ISF-H-BRS/SkinCam/Images/Software2.png

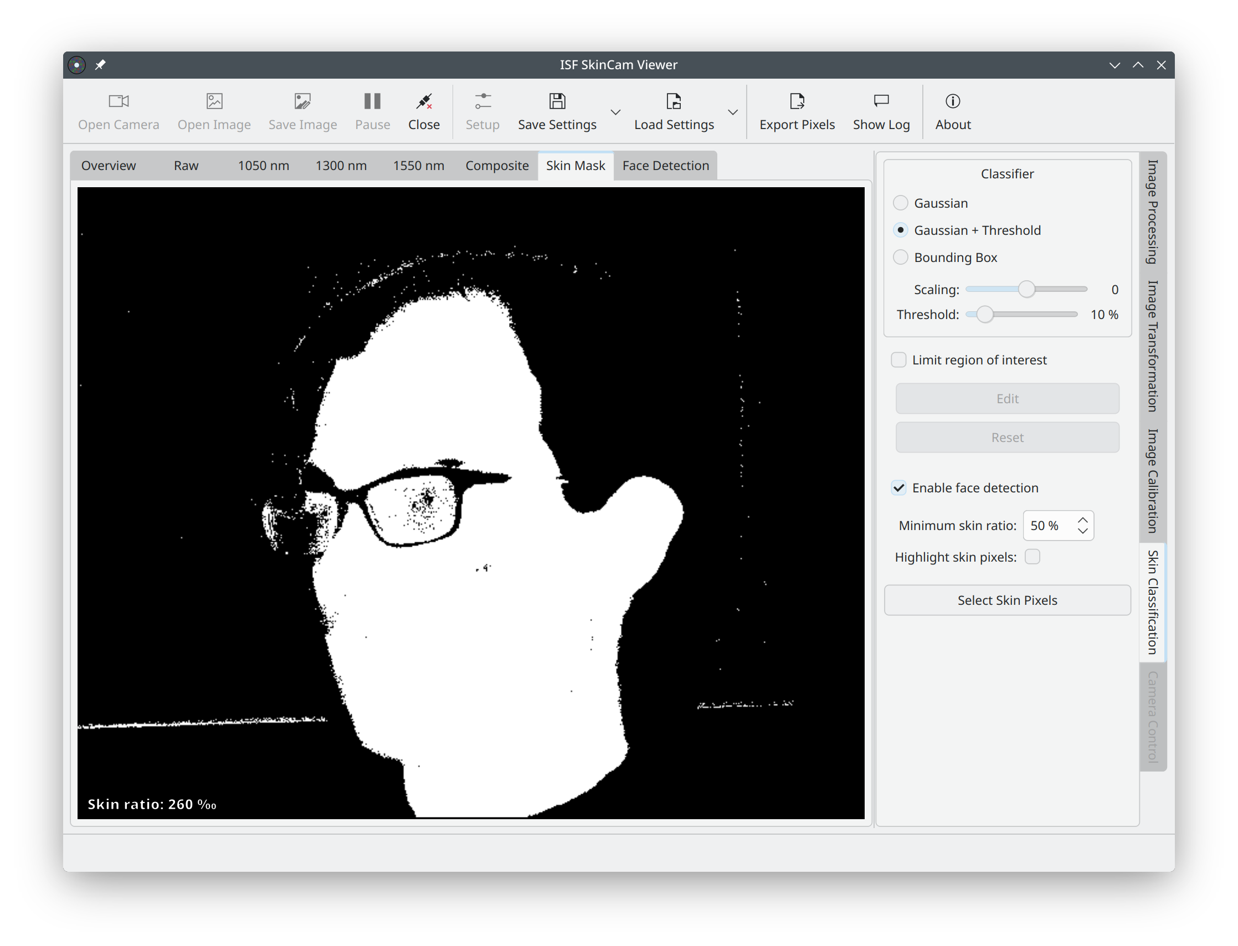
Images/Software2.png
