ISF-H-BRS/SkinCam/Data/Settings.ini

[Acquisition]
CameraGain=0
ExposureTime=5
FrameRate=40
IlluminationTime=5
TimesLocked=false

[Advanced]
TemperatureSetpoint=0

[Average]
Enabled=false
SampleCount=2

[Barrel]
Enabled=false
Factor=0

[Classifier]
Method=1
Scaling=0
Threshold=10

[ColorAdjustment]
Brightness=-5
Contrast=5
Enabled=false

[Crop]
Bottom=0
Enabled=false
Left=0
Right=0
Top=0

[DetectionThresholds]
SkinRatio=240

[FaceDetection]
Enabled=true
MinimumSkinRatio=50
SkinPixelsHighlighted=false

[ImageOutput]
Mirrored=false

[LedPower]
PowerLevel0=70
PowerLevel1=70
PowerLevel2=70

[RegionOfInterest]
Enabled=false
Vertex0=@Point(80 64)
Vertex1=@Point(560 64)
Vertex2=@Point(560 448)
Vertex3=@Point(80 448)

[Setup]
ControllerPort=
Renderer=Software
SaveOnExit=true
SerialNumber=
ServerEnabled=false
ServerPort=5432
ThreadCount=1

[Sharpening]
Amount=6
Enabled=false
Radius=1
Threshold=0

[SkinClassification]
Mean0=0.19982868432998657
Mean1=0.5167567729949951
Mean2=0.3540053963661194
Variance0=0.0007745716720819473
Variance1=0.0021819223184138536
Variance2=0.00274429633282125

[Smoothing]
Enabled=false
Radius=1

[Transformation]
Enabled=false
HScale=1
HShift=0
RAngle=0
VScale=1
VShift=0

[WhiteCalibration]
Enabled=true
Factor0=0.0439
Factor1=0.0648
Factor2=0.0697
