ISF-H-BRS/SkinCam/Firmware/Ringlight/src/ringlight.cpp

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
#include "ringlight.h"

#include <avr/interrupt.h>
#include <util/delay.h>

#include <stdlib.h>
#include <string.h>

// ---------------------------------------------------------------------------------------------- //

namespace {
    constexpr size_t ChannelIndex1050 = 0;
    constexpr size_t ChannelIndex1300 = 2;
    constexpr size_t ChannelIndex1550 = 3;

    constexpr size_t TriggerDuration = 30;
    constexpr size_t FrameDuration = 100;
    constexpr size_t SequenceDuration = 400;

    constexpr size_t MinimumSequenceDelay =   0;
    constexpr size_t MaximumSequenceDelay = 600;

    constexpr double TickDurationMs = 0.1;
}

// ---------------------------------------------------------------------------------------------- //

Ringlight::Ringlight()
    : m_interface(this)
{
}

// ---------------------------------------------------------------------------------------------- //

void Ringlight::exec()
{
    sei(); // Enable interrupts

    while (true)
        m_interface.update();
}

// ---------------------------------------------------------------------------------------------- //

void Ringlight::onCommandReceived(const char* command)
{
    m_led.setEnabled(LedControl::Channel::Status, true);

    if (strcmp(command, "S") == 0)
        protocolRunSequence();
    else if (strcmp(command, "P") == 0)
        protocolAnswerPing();
    else if (command[0] == 'D')
        protocolSetSequenceDelay(&command[1]);
    else
        sendError();

    m_led.setEnabled(LedControl::Channel::Status, false);
}

// ---------------------------------------------------------------------------------------------- //

void Ringlight::protocolRunSequence()
{
    sendAck();

    captureDark();
    captureChannel(ChannelIndex1050);
    captureChannel(ChannelIndex1300);
    captureChannel(ChannelIndex1550);

    delayTicks(m_sequenceDelay);
}

// ---------------------------------------------------------------------------------------------- //

void Ringlight::protocolAnswerPing()
{
    sendAck();
}

// ---------------------------------------------------------------------------------------------- //

void Ringlight::protocolSetSequenceDelay(const char* string)
{
    long int delay = atol(string);

    if (delay < MinimumSequenceDelay || delay > MaximumSequenceDelay)
        sendError();
    else
    {
        m_sequenceDelay = static_cast<size_t>(delay);
        sendAck();
    }
}

// ---------------------------------------------------------------------------------------------- //

inline
void Ringlight::sendAck()
{
    m_interface.sendMessage("A");
}

// ---------------------------------------------------------------------------------------------- //

inline
void Ringlight::sendError()
{
    m_interface.sendMessage("E");
}

// ---------------------------------------------------------------------------------------------- //

void Ringlight::captureDark()
{
    m_trigger.setActive(true);

    delayTicks(TriggerDuration);

    m_trigger.setActive(false);

    delayTicks(FrameDuration - TriggerDuration);
}

// ---------------------------------------------------------------------------------------------- //

void Ringlight::captureChannel(size_t channel)
{
    m_nir.enableChannel(channel);
    m_trigger.setActive(true);

    delayTicks(TriggerDuration);

    m_trigger.setActive(false);

    delayTicks(FrameDuration - TriggerDuration);

    m_nir.disableChannel(channel);
}

// ---------------------------------------------------------------------------------------------- //

inline
void Ringlight::delayTicks(size_t ticks)
{
    for (size_t i = 0; i < ticks; ++i)
        _delay_ms(TickDurationMs);
}

// ---------------------------------------------------------------------------------------------- //
