ISF-H-BRS/SkinCam/Software/SkinCam/mainwindow/classifierwidget.cpp

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
#include "classifierwidget.h"
#include "ui_classifierwidget.h"

// ---------------------------------------------------------------------------------------------- //

using namespace SkinCam;

// ---------------------------------------------------------------------------------------------- //

ClassifierWidget::ClassifierWidget(QWidget* parent)
    : QWidget(parent),
      m_ui(std::make_unique<Ui::ClassifierWidget>())
{
    m_ui->setupUi(this);

    m_ui->scalingNumber->setMinimumTextWidth("-100");

    m_ui->thresholdNumber->setSuffix(" %");
    m_ui->thresholdNumber->setMinimumTextWidth("100 %");

    connect(m_ui->gaussianButton, SIGNAL(clicked()), this, SLOT(onClassifierChanged()));
    connect(m_ui->gaussianThresholdButton, SIGNAL(clicked()), this, SLOT(onClassifierChanged()));
    connect(m_ui->boundingBoxButton, SIGNAL(clicked()), this, SLOT(onClassifierChanged()));

    connect(m_ui->scalingSlider, SIGNAL(valueChanged(int)),
            m_ui->scalingNumber, SLOT(setValue(int)));
    connect(m_ui->scalingSlider, SIGNAL(valueChanged(int)),
            this, SIGNAL(scalingChanged(int)));

    connect(m_ui->thresholdSlider, SIGNAL(valueChanged(int)),
            m_ui->thresholdNumber, SLOT(setValue(int)));
    connect(m_ui->thresholdSlider, SIGNAL(valueChanged(int)),
            this, SIGNAL(thresholdChanged(int)));
}

// ---------------------------------------------------------------------------------------------- //

ClassifierWidget::~ClassifierWidget() = default;

// ---------------------------------------------------------------------------------------------- //

void ClassifierWidget::applySettings(const Settings::ClassifierGroup& settings)
{
    setCurrentMethod(static_cast<SkinClassifier::Method>(settings.getMethod()));
    m_ui->scalingSlider->setValue(settings.getScaling());
    m_ui->thresholdSlider->setValue(settings.getThreshold());
}

// ---------------------------------------------------------------------------------------------- //

void ClassifierWidget::storeSettings(Settings::ClassifierGroup* settings)
{
    settings->setMethod(static_cast<int>(currentMethod()));
    settings->setScaling(m_ui->scalingSlider->value());
    settings->setThreshold(m_ui->thresholdSlider->value());
}

// ---------------------------------------------------------------------------------------------- //

void ClassifierWidget::setCurrentMethod(SkinClassifier::Method method)
{
    if (method == SkinClassifier::Method::Gaussian)
        m_ui->gaussianButton->setChecked(true);
    else if (method == SkinClassifier::Method::GaussianThreshold)
        m_ui->gaussianThresholdButton->setChecked(true);
    else
        m_ui->boundingBoxButton->setChecked(true);

    onClassifierChanged();
}

// ---------------------------------------------------------------------------------------------- //

auto ClassifierWidget::currentMethod() const -> SkinClassifier::Method
{
    if (m_ui->gaussianButton->isChecked())
        return SkinClassifier::Method::Gaussian;

    if (m_ui->gaussianThresholdButton->isChecked())
        return SkinClassifier::Method::GaussianThreshold;

    return SkinClassifier::Method::BoundingBox;
}

// ---------------------------------------------------------------------------------------------- //

auto ClassifierWidget::scaling() const -> int
{
    return m_ui->scalingSlider->value();
}

// ---------------------------------------------------------------------------------------------- //

auto ClassifierWidget::threshold() const -> int
{
    return m_ui->thresholdSlider->value();
}

// ---------------------------------------------------------------------------------------------- //

void ClassifierWidget::onClassifierChanged()
{
    const SkinClassifier::Method method = currentMethod();
    const bool isGaussian = (method == SkinClassifier::Method::Gaussian);

    m_ui->thresholdLabel->setEnabled(!isGaussian);
    m_ui->thresholdWidget->setEnabled(!isGaussian);

    emit classifierChanged(currentMethod());
}

// ---------------------------------------------------------------------------------------------- //
