ISF-H-BRS/SkinCam/Software/SkinCam/mainwindow/ledpowerwidget.cpp

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
#ifndef SKINCAM_BUILD_LEGACY

// ---------------------------------------------------------------------------------------------- //

#include "camerasystem.h"
#include "ledpowerwidget.h"

#include "ui_ledpowerwidget.h"

// ---------------------------------------------------------------------------------------------- //

using namespace SkinCam;

// ---------------------------------------------------------------------------------------------- //

LedPowerWidget::LedPowerWidget(QWidget* parent)
    : QWidget(parent),
      m_ui(std::make_unique<Ui::LedPowerWidget>())
{
    m_ui->setupUi(this);

    m_ui->label0->setSuffix(" %");
    m_ui->label1->setSuffix(" %");
    m_ui->label2->setSuffix(" %");

    m_ui->label0->setMinimumTextWidth("100 %");
    m_ui->label1->setMinimumTextWidth("100 %");
    m_ui->label2->setMinimumTextWidth("100 %");

    connect(m_ui->slider0, SIGNAL(valueChanged(int)), m_ui->label0, SLOT(setValue(int)));
    connect(m_ui->slider1, SIGNAL(valueChanged(int)), m_ui->label1, SLOT(setValue(int)));
    connect(m_ui->slider2, SIGNAL(valueChanged(int)), m_ui->label2, SLOT(setValue(int)));

    connect(m_ui->slider0, SIGNAL(valueChanged(int)), this, SLOT(handleLevelChange()));
    connect(m_ui->slider1, SIGNAL(valueChanged(int)), this, SLOT(handleLevelChange()));
    connect(m_ui->slider2, SIGNAL(valueChanged(int)), this, SLOT(handleLevelChange()));

    connect(m_ui->resetButton, SIGNAL(clicked()), this, SLOT(resetValues()));
}

// ---------------------------------------------------------------------------------------------- //

LedPowerWidget::~LedPowerWidget() = default;

// ---------------------------------------------------------------------------------------------- //

void LedPowerWidget::applySettings(const Settings::LedPowerGroup& settings)
{
    blockSignals(true);
    m_ui->slider0->setValue(settings.getPowerLevel0());
    m_ui->slider1->setValue(settings.getPowerLevel1());
    m_ui->slider2->setValue(settings.getPowerLevel2());
    blockSignals(false);

    handleLevelChange();
}

// ---------------------------------------------------------------------------------------------- //

void LedPowerWidget::storeSettings(Settings::LedPowerGroup* settings)
{
    settings->setPowerLevel0(m_ui->slider0->value());
    settings->setPowerLevel1(m_ui->slider1->value());
    settings->setPowerLevel2(m_ui->slider2->value());
}

// ---------------------------------------------------------------------------------------------- //

auto LedPowerWidget::getPowerLevel0() const -> int
{
    return m_ui->slider0->value();
}

// ---------------------------------------------------------------------------------------------- //

auto LedPowerWidget::getPowerLevel1() const -> int
{
    return m_ui->slider1->value();
}

// ---------------------------------------------------------------------------------------------- //

auto LedPowerWidget::getPowerLevel2() const -> int
{
    return m_ui->slider2->value();
}

// ---------------------------------------------------------------------------------------------- //

void LedPowerWidget::handleLevelChange()
{
    if (signalsBlocked())
        return;

    int level0 = m_ui->slider0->value();
    int level1 = m_ui->slider1->value();
    int level2 = m_ui->slider2->value();

    emit powerLevelsChanged(level0, level1, level2);
}

// ---------------------------------------------------------------------------------------------- //

void LedPowerWidget::resetValues()
{
    blockSignals(true);
    m_ui->slider0->setValue(CameraSystem::DefaultPowerLevel);
    m_ui->slider1->setValue(CameraSystem::DefaultPowerLevel);
    m_ui->slider2->setValue(CameraSystem::DefaultPowerLevel);
    blockSignals(false);

    handleLevelChange();
}

// ---------------------------------------------------------------------------------------------- //

#endif // !SKINCAM_BUILD_LEGACY

// ---------------------------------------------------------------------------------------------- //
