ISF-H-BRS/SkinCam/Software/SkinCam/camerasystem.h

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
#pragma once

#include "camera.h"
#include "controller.h"
#include "dummycamera.h"
#include "imageprovider.h"

SKINCAM_BEGIN_NAMESPACE();

class CameraSystem : public ImageProvider
{
public:
    static constexpr int MinimumRefreshRate =
            1'000'000 / Controller::MaximumSequenceDuration.count();

    static constexpr int MaximumRefreshRate =
            1'000'000 / Controller::MinimumSequenceDuration.count();

    static constexpr int DefaultRefreshRate =
            1'000'000 / Controller::DefaultSequenceDuration.count();

    static constexpr auto MinimumIlluminationTime = Controller::MinimumIlluminationTime;
    static constexpr auto MaximumIlluminationTime = Controller::MaximumIlluminationTime;
    static constexpr auto DefaultIlluminationTime = Controller::DefaultIlluminationTime;

#ifndef SKINCAM_BUILD_LEGACY
    static constexpr auto DefaultPowerLevel = Controller::DefaultPowerLevel;
#endif

    struct Setup
    {
        Camera::Setup cameraSetup;

        int refreshRate = DefaultRefreshRate;
        std::chrono::microseconds illuminationTime = DefaultIlluminationTime;

#ifdef SKINCAM_BUILD_LEGACY
        std::string controllerPort;
#else
        int powerLevel0 = DefaultPowerLevel;
        int powerLevel1 = DefaultPowerLevel;
        int powerLevel2 = DefaultPowerLevel;
#endif
    };

public:
    CameraSystem(const Setup& setup);

    void start() override;
    void stop() override;

    auto getMinRefreshRate() const -> int override;
    auto getMaxRefreshRate() const -> int override;

    void setRefreshRate(int rate) override;
    auto getRefreshRate() const -> int override;

    void getNextFrame(MemoryBuffer1w* dark, MemoryBuffer1w* channel0,
                      MemoryBuffer1w* channel1, MemoryBuffer1w* channel2) override;

    void setIlluminationTime(std::chrono::microseconds us);
    auto getIlluminationTime() const -> std::chrono::microseconds;

#ifndef SKINCAM_BUILD_LEGACY
    void setPowerLevels(int level0, int level1, int level2);
    auto getPowerLevels() const -> std::tuple<int,int,int>;

    auto getPowerStatus() const -> Controller::PowerStatus;
#endif

    void setExposureTime(std::chrono::microseconds time);
    void setGain(Camera::Gain gain);
    void setTemperatureSetpoint(Camera::TemperatureSetpoint point);

    auto getCameraStatus() const -> Camera::Status;

    static auto getAvailableCameras() -> std::vector<std::string>;
    static auto isCameraAvailable(const std::string& serial) -> bool;

private:
    void setSequenceConfiguration(int refreshRate, std::chrono::microseconds illuminationTime);

private:
#ifdef SKINCAM_ENABLE_VIMBA
    AVT::VmbAPI::VimbaSystem* m_system;
#endif

#if !defined(SKINCAM_ENABLE_VIMBA) || defined(SKINCAM_USE_DUMMY_CAMERA)
    DummyCameraPtr m_camera;
#else
    CameraPtr m_camera;
#endif

    ControllerPtr m_controller;

    int m_refreshRate = DefaultRefreshRate;
    std::chrono::microseconds m_illuminationTime = DefaultIlluminationTime;

    mutable std::mutex m_mutex;
};

SKINCAM_END_NAMESPACE();
