ISF-H-BRS/SkinCam/Software/SkinCam/assertions.h

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
#pragma once

#include "namespace.h"

#include <algorithm>
#include <chrono>
#include <iostream>

SKINCAM_BEGIN_NAMESPACE();

namespace Assertions {

void fail(const char* condition, const char* function, const char* file, int line);

void notifySatisfied(const char* condition, const char* function);
void notifyUnsatisfied(const char* condition, const char* function);

void notifyIgnoreNull(const char* function, const char* ptrarg);
void notifyIgnoreNotNull(const char* function, const char* ptrarg);

inline
auto operator<<(std::ostream& os, std::chrono::microseconds us) -> std::ostream&
{
    os << us.count() << " µs";
    return os;
}

template <typename T>
void clampToRange(T& value, const T& min, const T& max, const char* function)
{
    T newValue = std::clamp(value, min, max);

    std::cerr << "In function " << function << ": Value " << value
              << " is outside range (" << min << "," << max << "). "
              << "Clamping to " << newValue << "." << std::endl;

    value = newValue;
}

template <typename T>
void notifyIgnoreOutOfRange(const T& value, const T& min, const T& max, const char* function)
{
    std::cerr << "In function " << function << ": Value " << value
              << " is outside range (" << min << "," << max << "). "
              << "Aborting function call." << std::endl;
}

} // End of namespace Assertions


#ifdef NDEBUG
#define ASSERT(condition)
#else
#define ASSERT(condition) \
    if (!(condition)) Assertions::fail(#condition, __PRETTY_FUNCTION__, __FILE__, __LINE__)
#endif

#define ASSERT_NULL(p) ASSERT((p) == nullptr)
#define ASSERT_NOT_NULL(p) ASSERT((p) != nullptr)
#define ASSERT_IN_RANGE(value, min, max) ASSERT((value) >= (min) && (value) <= (max))


#ifdef NDEBUG
#define CLAMP_TO_RANGE(value, min, max) \
    if (value < min || value > max) Assertions::clampToRange(value, min, max, __PRETTY_FUNCTION__)
#else
#define CLAMP_TO_RANGE(value, min, max) ASSERT_IN_RANGE(value, min, max)
#endif


#ifdef NDEBUG
#define RETURN_IF(condition) \
    if (condition) return Assertions::notifySatisfied(#condition, __PRETTY_FUNCTION__)
#else
#define RETURN_IF(condition) ASSERT(!(condition))
#endif


#ifdef NDEBUG
#define RETURN_IF_NOT(condition) \
    if (!(condition)) return Assertions::notifyUnsatisfied(#condition, __PRETTY_FUNCTION__)
#else
#define RETURN_IF_NOT(condition) ASSERT(condition)
#endif


#ifdef NDEBUG
#define RETURN_IF_OUT_OF_RANGE(value, min, max) \
    if (value < min || value > max) \
        return Assertions::notifyIgnoreOutOfRange(value, min, max, __PRETTY_FUNCTION__))
#else
#define RETURN_IF_OUT_OF_RANGE(value, min, max) ASSERT_IN_RANGE(value, min, max)
#endif


#ifdef NDEBUG
#define RETURN_IF_NULL(ptr) \
    if ((ptr) == nullptr) return Assertions::notifyIgnoreNull(__PRETTY_FUNCTION__, #ptr)
#else
#define RETURN_IF_NULL(ptr) ASSERT_NOT_NULL(ptr)
#endif


#ifdef NDEBUG
#define RETURN_IF_NOT_NULL(ptr) \
    if ((ptr) != nullptr) return Assertions::notifyIgnoreNotNull(__PRETTY_FUNCTION__, #ptr)
#else
#define RETURN_IF_NOT_NULL(ptr) ASSERT_NULL(ptr)
#endif

SKINCAM_END_NAMESPACE();
