ISF-H-BRS/SkinCam/Software/SkinCam/mainwindow/acquisitionwidget.h

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
#pragma once

#include "camerasystem.h"
#include "namespace.h"
#include "settings.h"

#include <QWidget>

namespace Ui {
    class AcquisitionWidget;
}

SKINCAM_BEGIN_NAMESPACE();

constexpr auto millisecondsToTime(double ms) -> std::chrono::microseconds {
    return std::chrono::microseconds(static_cast<long>(ms * 1000.0));
}

constexpr auto timeToMilliseconds(std::chrono::microseconds time) -> double {
    return static_cast<double>(time.count()) / 1000.0;
}

class AcquisitionWidget : public QWidget
{
    Q_OBJECT

public:
    explicit AcquisitionWidget(QWidget* parent = nullptr);
    ~AcquisitionWidget() override;

    void applySettings(const Settings::AcquisitionGroup& settings);
    void storeSettings(Settings::AcquisitionGroup* settings);

    void setMinMaxFrameRate(int minimum, int maximum);

    auto getFrameRate() const -> int;
    auto getIlluminationTime() const -> std::chrono::microseconds;
    auto getExposureTime() const -> std::chrono::microseconds;
    auto getCameraGain() const -> Camera::Gain;

signals:
    void frameRateChanged(int rate);
    void illuminationTimeChanged(std::chrono::microseconds us);
    void exposureTimeChanged(std::chrono::microseconds us);
    void cameraGainChanged(Camera::Gain gain);

private slots:
    void handleFrameRateChange(int value);
    void handleIlluminationTimeChange(double value);
    void handleExposureTimeChange(double value);
    void handleLockButtonClicked();
    void handleCameraGainChange(int index);

    void resetValues();

private:
    void setTimesLocked(bool lock);

    static constexpr auto MinimumFrameRate = CameraSystem::MinimumRefreshRate;
    static constexpr auto MaximumFrameRate = CameraSystem::MaximumRefreshRate;

    static constexpr double MinimumIlluminationTime =
                                        timeToMilliseconds(CameraSystem::MinimumIlluminationTime);
    static constexpr double MaximumIlluminationTime =
                                        timeToMilliseconds(CameraSystem::MaximumIlluminationTime);

    static constexpr double MinimumExposureTime = timeToMilliseconds(Camera::MinimumExposureTime);
    static constexpr double MaximumExposureTime = timeToMilliseconds(Camera::MaximumExposureTime);

private:
    std::unique_ptr<Ui::AcquisitionWidget> m_ui;
    bool m_timesLocked = false;
};

SKINCAM_END_NAMESPACE();
